ioquatix/matx-case/parts/duct.scad

include <../source/case.scad>;

duct();
