ioquatix/matx-case/parts/fan_bracket.scad

include <../source/case.scad>;

fan_bracket(thickness=1);
