ioquatix/matx-case/parts/pci_rear_bracket_bottom.scad

include <../source/case.scad>;

render()
pci_rear_bracket_bottom();
