ioquatix/matx-case/parts/pci_rear_bracket_top.scad

include <../source/case.scad>;

pci_rear_bracket_top();
