ioquatix/matx-case/parts/pci_rear_slots.scad

include <../source/case.scad>;

pci_rear_slots();
//atx_io_support();
