ioquatix/matx-case/parts/ssd.scad

include <../source/case.scad>;

ssd_cage(bays=1);
